wlellington/LiquidRedox/firmware/status_led.py

from kmk.extensions import Extension
from kmk.scheduler import create_task, cancel_task
from kmk.modules.layers import Layers
from kmk.extensions.lock_status import LockStatus
from kmk.modules.dynamic_sequences import DynamicSequences, SequenceStatus
from kmk.extensions.RGB import RGB as _RGB

# This class only expects the static color mode to be used, will probably do weird things
#   if real animations are plaing
class RGB(_RGB):
    # Write any combination of HSV to single index, leave value alone (use self.hue etc) otherwise
    #   For example, hue and sat can be provided to change color, but val left alone to maintain brightness
    def set_static_led(
                    self,
                    hue: int = None,
                    sat: int = None,
                    val: int = None,
                    index: int = 0):

        if hue is None:
            hue = self.hue
        if sat is None:
            sat = self.sat
        if val is None:
            val = self.val

        self.set_hsv(hue, sat, val, index)

        try:
            self.curr_colors[index] = (hue, sat, val)
        except Exception as E:
            self.curr_colors = {}
            self.curr_colors[index] = (hue, sat, val)

        #print("Saved {}: {}".format(index, self.curr_colors[index]))

# Constant values just to clean up code a bit, add your own here!
class CustomColors:
    AMBER   = ( 8, 255, 100)
    PRICKLY = (253, 255, 100)
    DEEP    = (180, 255, 100)
    DRIFT   = (105, 255, 100)
    WHITE   = (  0,   0, 100)
    BLIND   = (  0,   0, 200)
    OFF     = (  0,   0,   0)

    # Old RGB stuff - remove?
    #AMBER = (241, 136, 5, 0)
    #PRICKLY = (240, 2, 109, 0)
    #DEEP = (47, 65, 130, 0)
    #BLIND = (200, 200, 200, 200)jkl
    #OFF = (0, 0, 0, 0)

# Extension to update specific LEDs for status info
#   Currently this does:
#       - Layer Colors
#       - Caps + Num Lock
#       - DynamicSequence bindings
class LEDStatus(Extension):
    def __init__(self,
                keyboard = None,
                rgb: RGB = None,
                layers: Layers = None,
                layer_leds: list[int] = [],
                layer_colors: list[tuple] = [],
                locks: LockStatus = None,
                caps_lock_leds: list[int] = [],
                num_lock_leds: list[int] = [],
                dynamic_sequences: DynamicSequences = None,
                macro_leds: list[int] = [],
                ind_color_1: CustomColors = CustomColors.WHITE,
                ind_color_2: CustomColors = CustomColors.AMBER,
                ind_color_3: CustomColors = CustomColors.DEEP,
                sleep_minutes: int = None,
                sleep_leds: list[int] = [],
                ):
        self.keyboard = keyboard
        self.rgb = rgb

        self.layers = layers
        self.layer_leds = layer_leds
        self.layer_colors = layer_colors
        self._last_layer = 0

        self.locks = locks
        self.caps_lock_leds = caps_lock_leds
        self.num_lock_leds = num_lock_leds
        self._old_locks = None

        self.dynamic_sequences = dynamic_sequences
        self.macro_leds = macro_leds
        self._bound = []
        self._flashing = []
        self._flash_on = False
        self._flash_task = None

        self._asleep = False

        self.ind_color_1 = ind_color_1
        self.ind_color_2 = ind_color_2
        self.ind_color_3 = ind_color_3

        if sleep_minutes is None:
            self.sleep_ms = 1000 * 60 * 10
        else:
            self.sleep_ms = 1000 * 60 * sleep_minutes

        self.sleep_leds = sleep_leds
        self._asleep = False
        self._prev_asleep = False
        self._sleep_timer = create_task(self.enable_sleep, after_ms=(self.sleep_ms))

        self._old_colors = []

    # Set colors based on layer
    def _update_layers(self):
        update = False
        # Check if layer changed, if so update
        if self._last_layer != self.keyboard.active_layers[0]:
            self._last_layer = self.keyboard.active_layers[0]
            update = True
            color = self.layer_colors[self._last_layer]
            for index in self.layer_leds:
                self.rgb.set_static_led(color[0], color[1], None, index)

            # Update rgb object hue and at sat to match layer
            # This helps with glitches caused when using things like KC.RGB_VAI
            #   though some slightly glitchy things might still happen
            self.rgb.hue = color[0]
            self.rgb.sat = color[1]

            self.need_update = update

    # Update colors based on host lock status
    def _update_locks(self):

        # No update neede if locks not changed
        if self._old_locks == self.locks.report:
            return

        self._old_locks = self.locks.report
        update = True

        # Caps lock color logic
        if self.locks.get_caps_lock():
            for index in self.caps_lock_leds:
                color = self.ind_color_1
                self.rgb.set_static_led(color[0], color[1], None, index)
        else:
            for index in self.caps_lock_leds:
                color = CustomColors.OFF
                # This one needs the None so that the OFF color applies (zero bright)
                self.rgb.set_static_led(color[0], color[1], color[2], index)

        # Num lock color logic (Only applies to layer 2)
        if self.keyboard.active_layers[0] == 2:
            if self.locks.get_num_lock():
                for index in self.num_lock_leds:
                    color = self.ind_color_1
                    self.rgb.set_static_led(color[0], color[1], None, index)
            else:
                for index in self.num_lock_leds:
                    color = CustomColors.OFF
                    self.rgb.set_static_led(color[0], color[1], color[2], index)

        self.need_update = update

    # Update layer 1 information for matching dynamic_sequence macros
    def _update_macros(self):
        update = False
        status = self.dynamic_sequences.status
        current_ind = self.dynamic_sequences.current_ind

        # Only update if on layer 0
        if self.keyboard.active_layers[0] == 0:
            # Set bound macros to second color
            for x in range(4):
                # Check to see if sequence_data for a macro slot is populated
                #   Empty slots have 3 sequence frames in them, so if its longer than that, add color
                if len(self.dynamic_sequences.sequences[x+1].sequence_data) > 3:
                    color = self.ind_color_2
                    self.rgb.set_static_led(color[0], color[1], None, self.macro_leds[x])
                    if x not in self._bound:
                        self._bound.append(x)
                        self.need_update = True

            # Indicate slot key while recording
            if status == SequenceStatus.RECORDING:
                color = self.ind_color_1
                self.rgb.set_static_led(color[0], color[1], None, self.macro_leds[current_ind-1])
                self.need_update = True

    def _all_off(self):
        # Save old colors
        self._old_colors = self.rgb.curr_colors.copy()

        color = CustomColors.OFF
        for index in self.sleep_leds:
            self.rgb.set_static_led(color[0], color[1], color[2], index)

        self.need_update = True

    def _all_on(self):
        for index, color in self._old_colors.items():
            #print("Restoring {}: {}".format(index, color))
            self.rgb.set_static_led(color[0], color[1], color[2], index)
        self.need_update = True

    # Main update function
    def update_colors(self,):
        self.need_update = False

        # Turn everything off if asleep (only first time)
        if self._asleep and not self._prev_asleep:
            print("Sleeping leds...")
            self._all_off()
            self._prev_asleep = True

        # Turn things back on on waking
        elif self._prev_asleep and not self._asleep:
            print("Waking leds...")
            self._all_on()
            self._prev_asleep = False

        # If awake apply colors
        else:
            # Update layer colors
            self._update_layers()

            # Update lock colors
            self._update_locks()

            # Update macro colors
            if self.macro_leds:
                self._update_macros()


        # Force "animation update"
        if self.need_update:
            self.rgb.show()


    def on_runtime_enable(self, sandbox):
        return

    def on_runtime_disable(self, sandbox):
        return

    # Create scheduled task for updating colors
    def during_bootup(self, sandbox):
        self._task = create_task(self.update_colors, period_ms=100)

    def before_matrix_scan(self, sandbox):
        return

    def after_matrix_scan(self, sandbox):
        # Check if any keyboard updates occured, if not let the timer continue

        if sandbox.matrix_update or sandbox.secondary_matrix_update:
            self._asleep = False
            #since the task may not exist on startup or after sleeping, allow failure
            try:
                cancel_task(self._sleep_timer)
            except Exception as E:
                print("No Sleep Timer!")
                print(E)
            self._sleep_timer = create_task(self.enable_sleep, after_ms=(self.sleep_ms))
        return

    def before_hid_send(self, sandbox):
        return

    def after_hid_send(self, sandbox):
        return

    def on_powersave_enable(self, sandbox):
        self._asleep = True
        return

    # Not sure if necessary
    def on_powersave_disable(self, sandbox):
        self._asleep = False
        self._do_update()

    def deinit(self, sandbox):
        return

    # Set sleep state to true only when timer expires
    def enable_sleep(self):
        #print("SLEEPING!!!")
        self._asleep = True
        self._prev_asleep = False
